aid-lab-org/eTactileKit/1_Hardware/04_Resources/Capture1.PNG

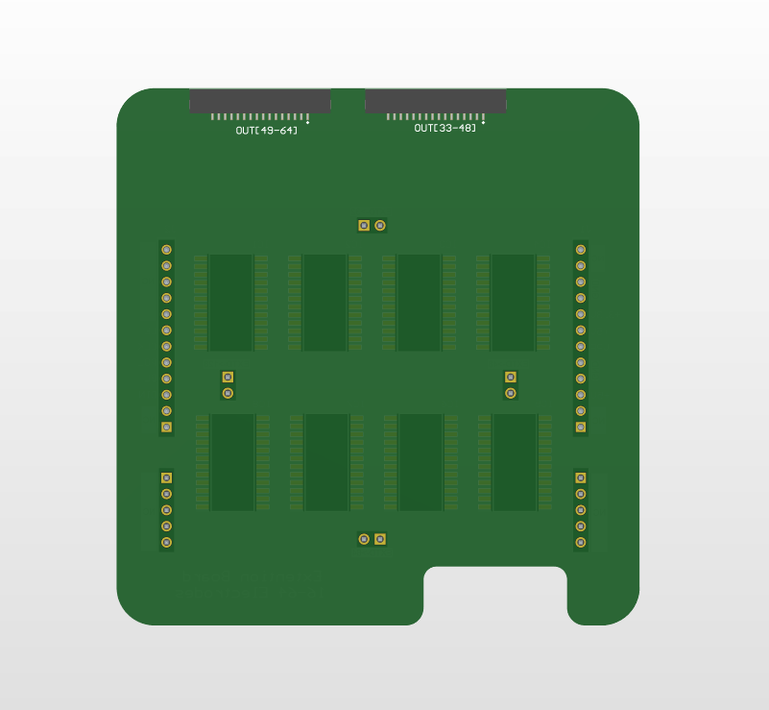
1_Hardware/04_Resources/Capture1.PNG
