aid-lab-org/eTactileKit/1_Hardware/04_Resources/Capture5.PNG

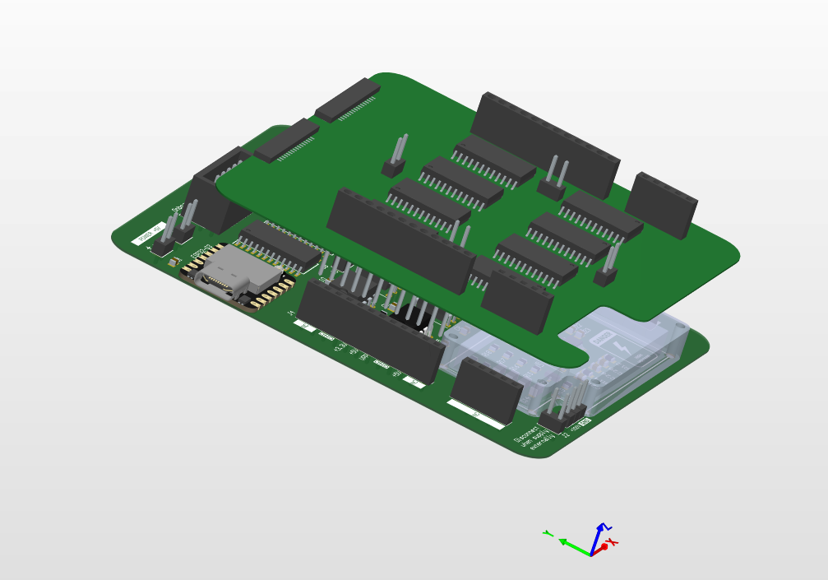
1_Hardware/04_Resources/Capture5.PNG
