aid-lab-org/eTactileKit/1_Hardware/04_Resources/Capture.PNG

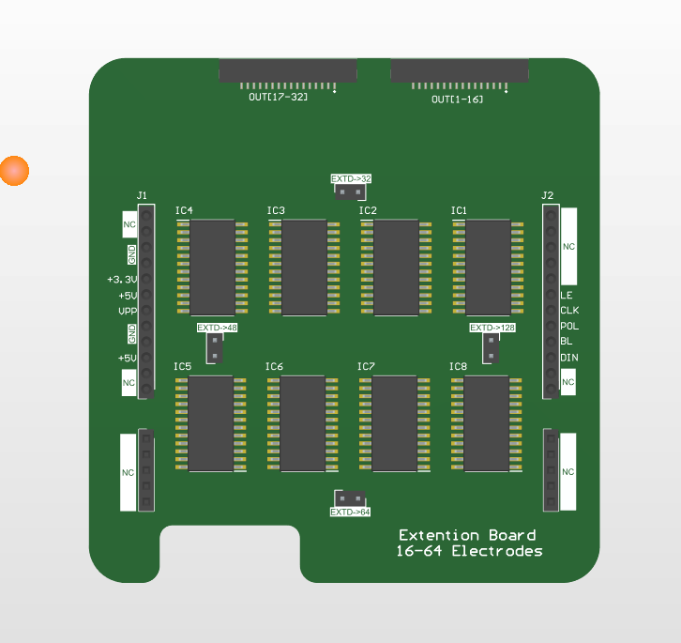
1_Hardware/04_Resources/Capture.PNG
