aid-lab-org/eTactileKit/8_Documentation/4_processing_gui/GUI.gif

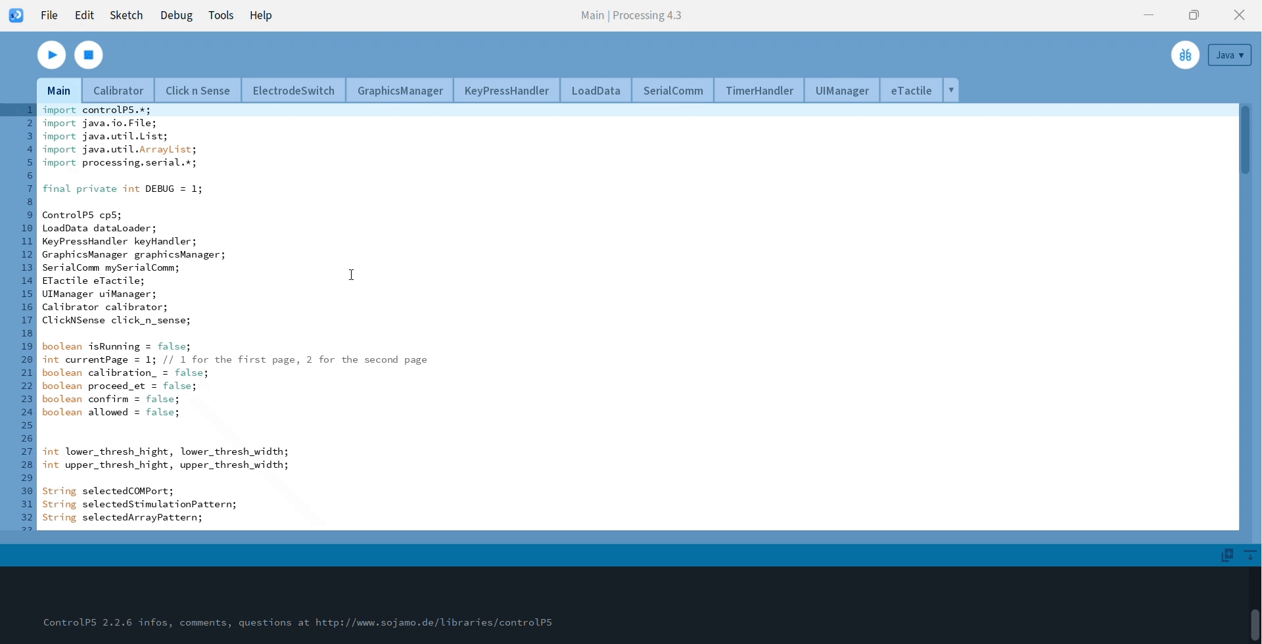
8_Documentation/4_processing_gui/GUI.gif
