aid-lab-org/eTactileKit/3_Electrode_Design_Tool/3_FabricationTool_App/images/finger_top.jpg

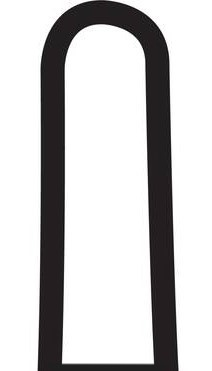
3_Electrode_Design_Tool/3_FabricationTool_App/images/finger_top.jpg
