aid-lab-org/eTactileKit/3_Electrode_Design_Tool/3_FabricationTool_App/images/Finger_Wrap_1.png

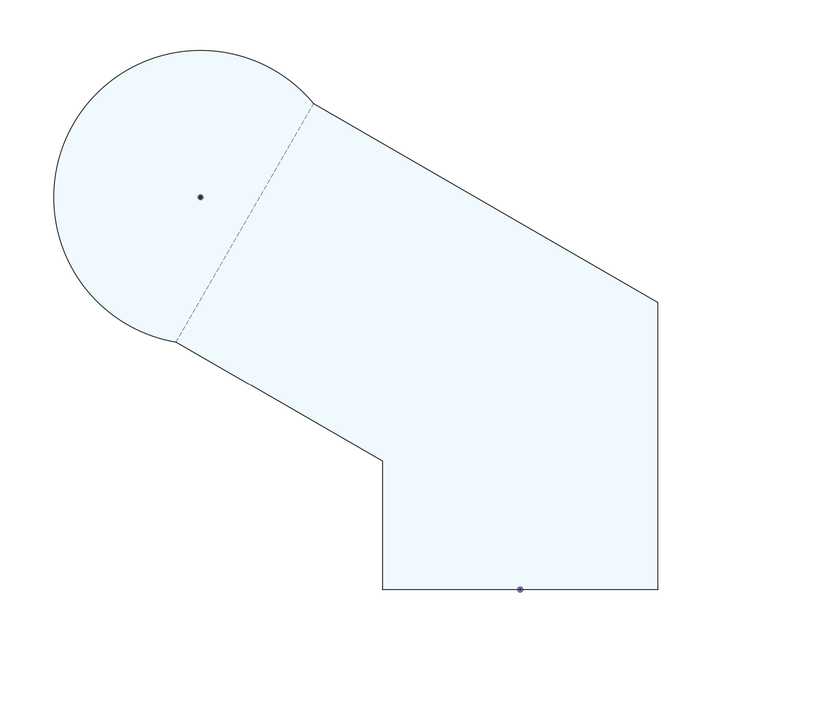
3_Electrode_Design_Tool/3_FabricationTool_App/images/Finger_Wrap_1.png
