aid-lab-org/eTactileKit/1_Hardware/04_Resources/Main_Controller_Schematic.pdf

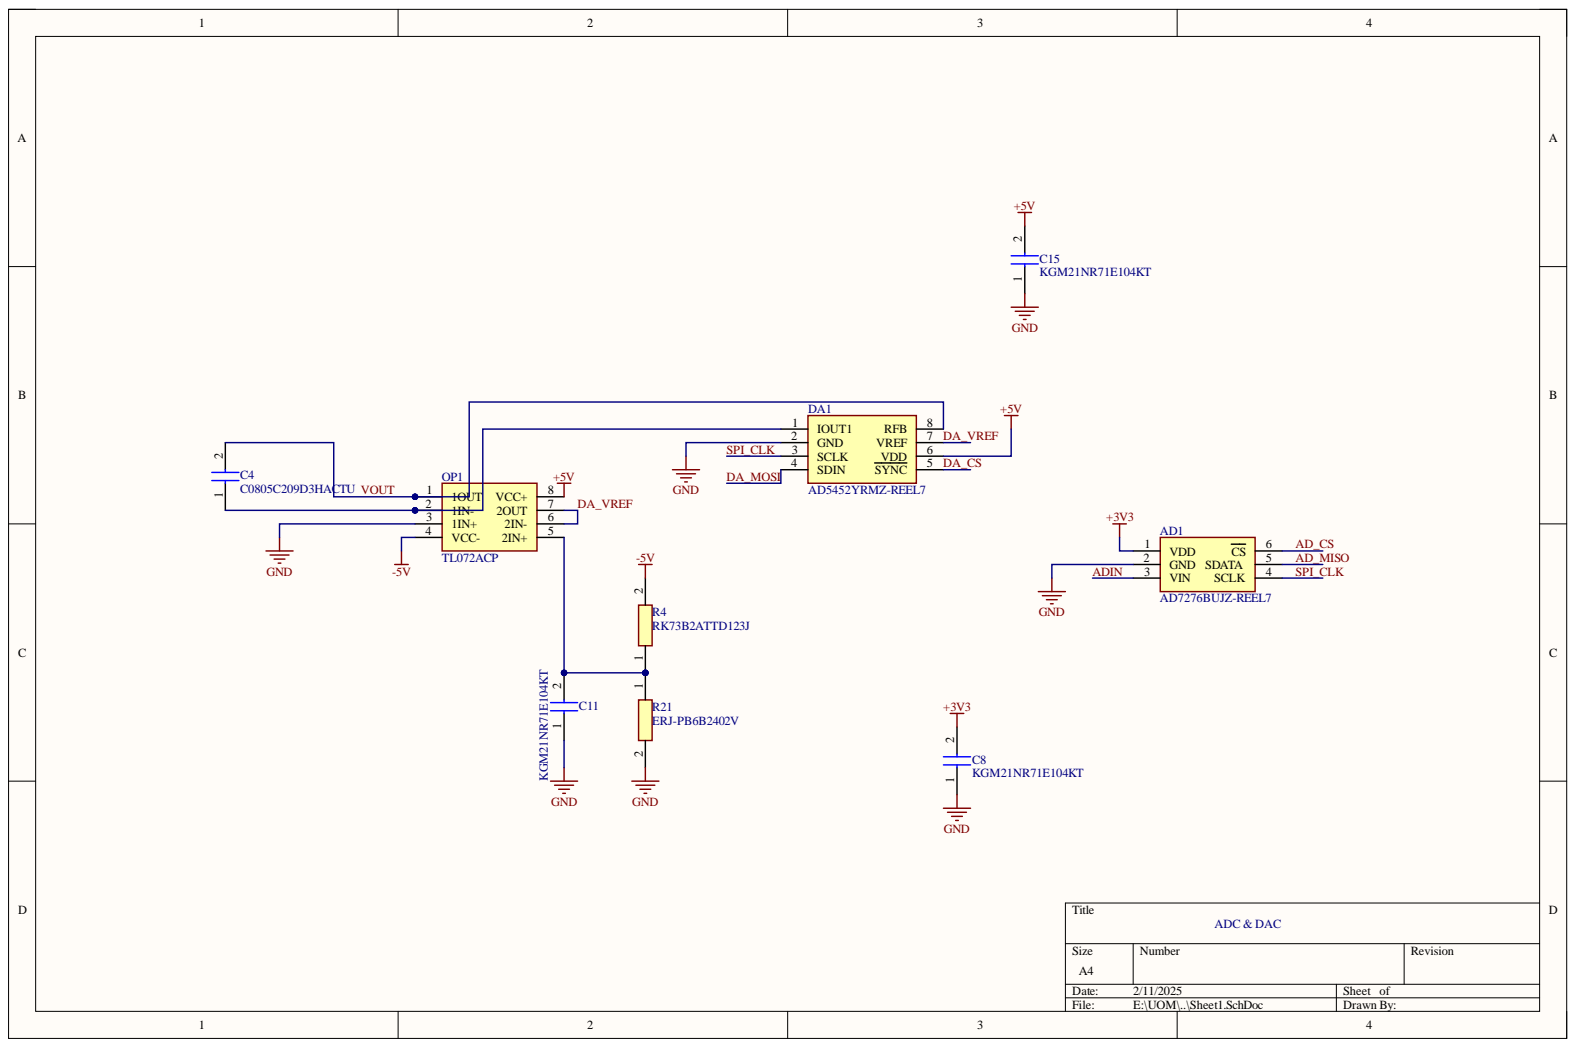
[picture p94: page 1]

Siz e A4 | Numb e r | R evisio n

Da te : 2/11/202 5 | She et of
File : E:\UOM\. .\She et1 . S c hD o c | Dr awn B y :

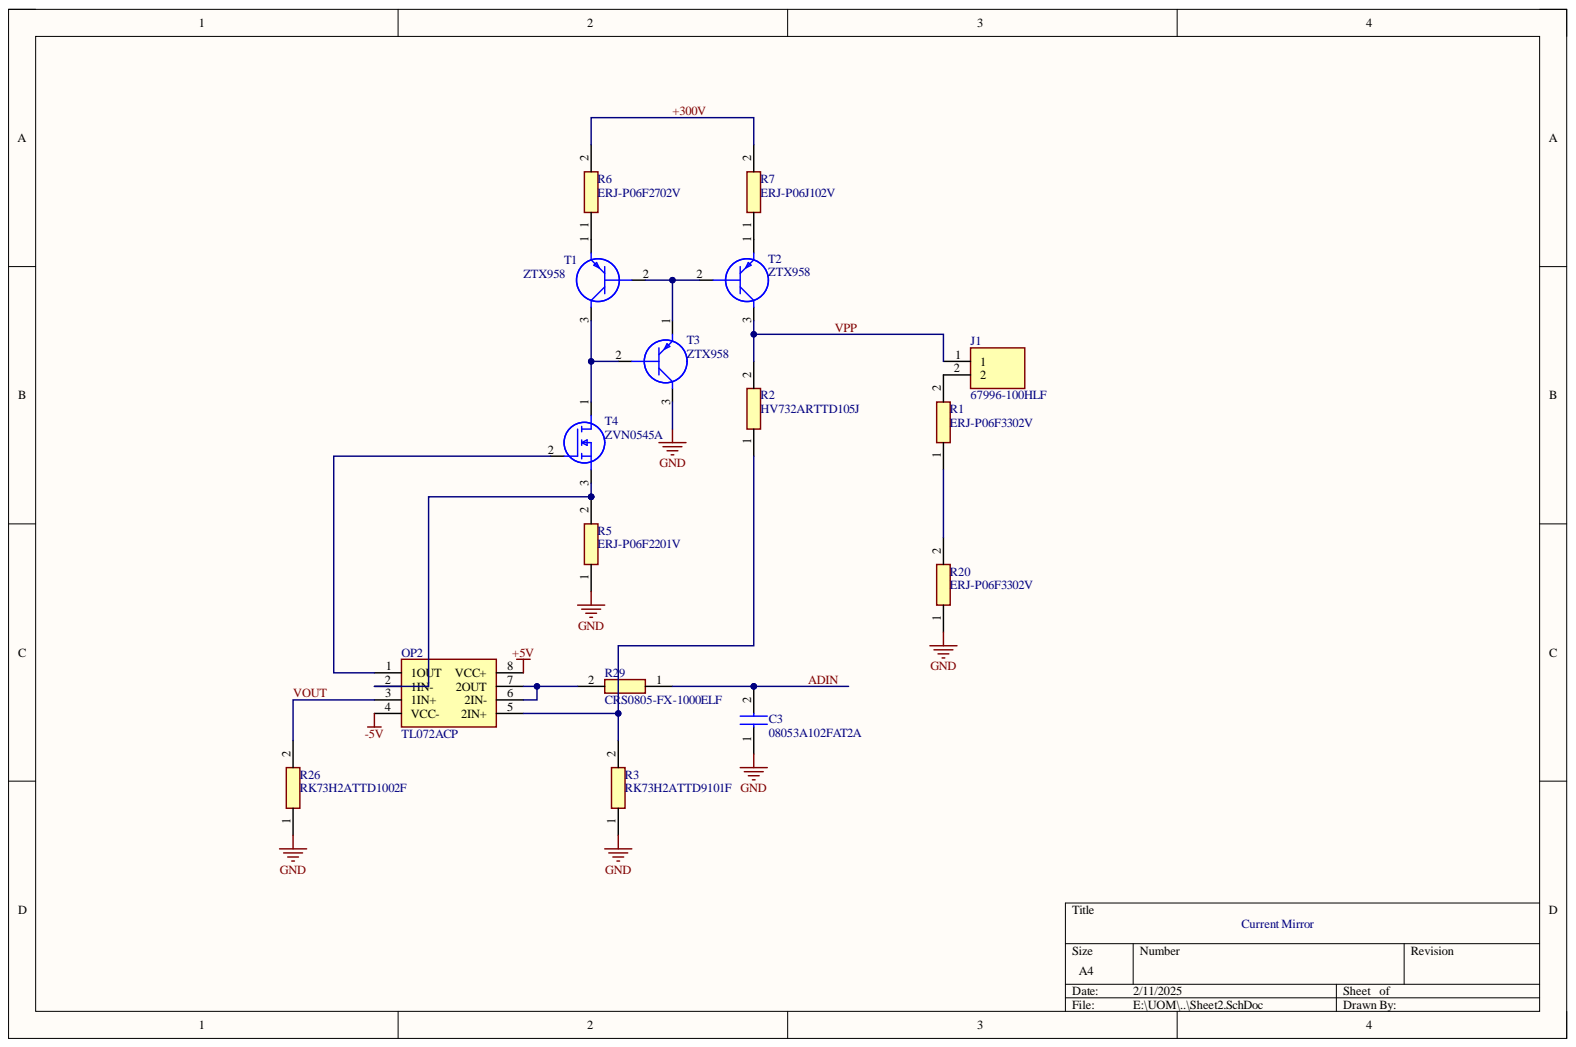
[picture p95: page 2]

Siz e A4 | Numb e r | R evisio n

Da te : 2/11/202 5 | She et of
File : E:\UOM\. .\She et2 . S c hD o c | Dr awn B y :

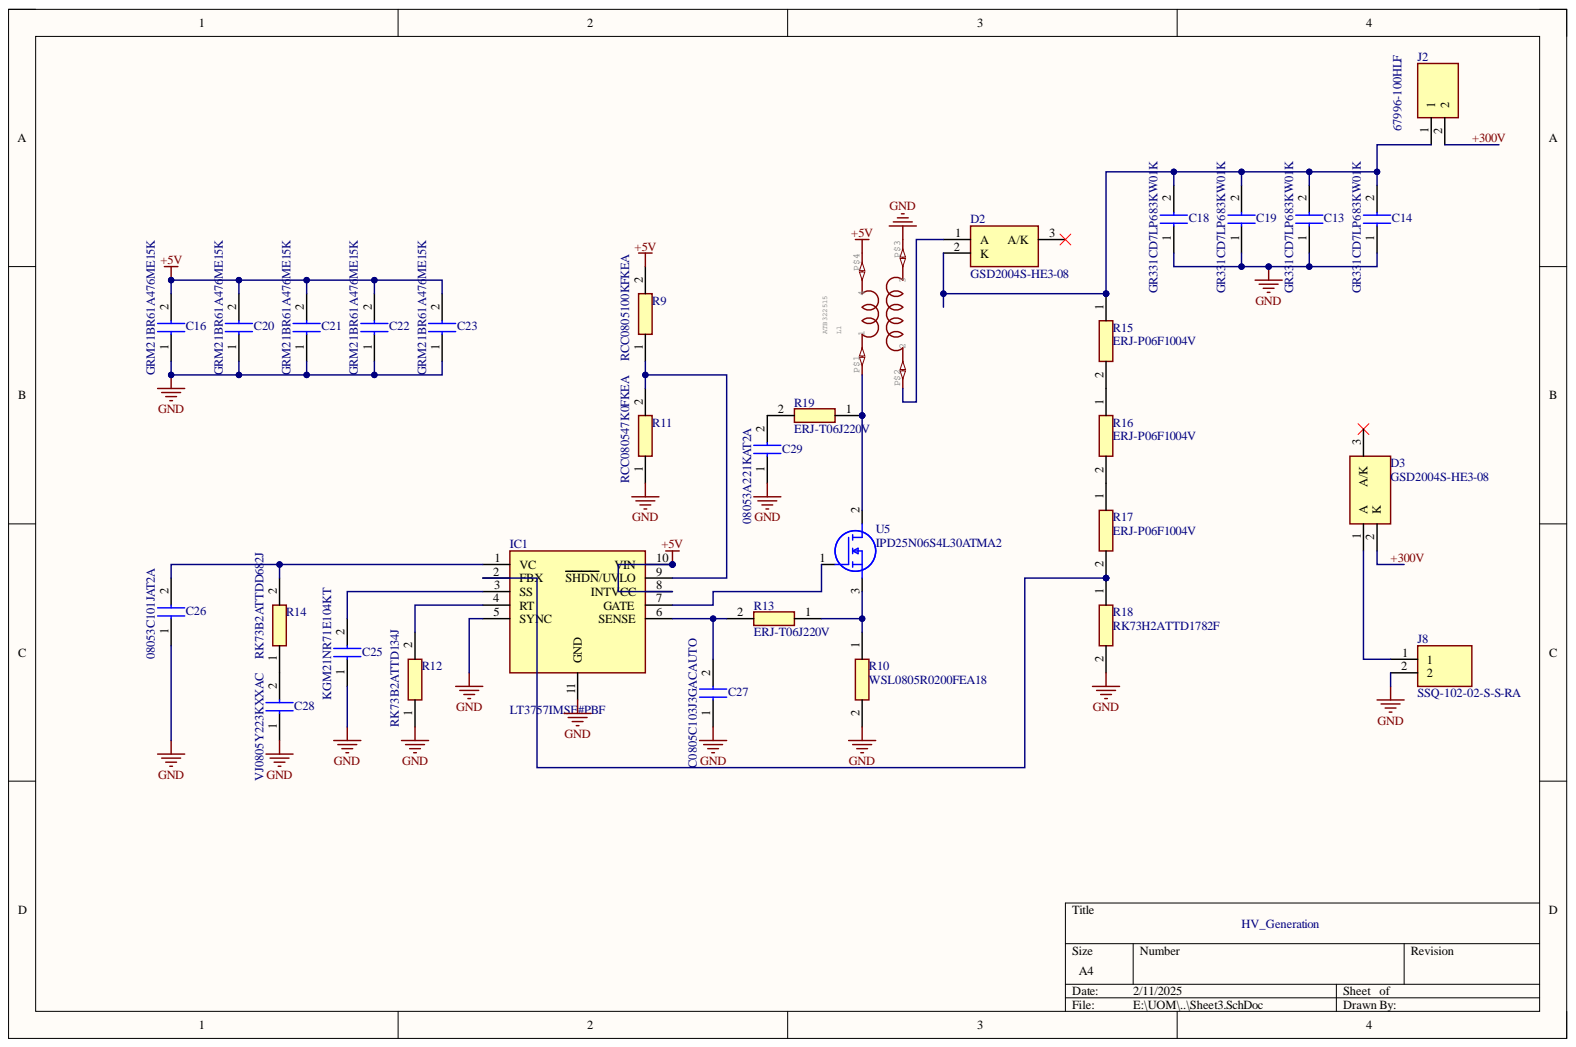
[picture p96: page 3]

Siz e A4 | Numb e r | R evisio n

Da te : 2/11/202 5 | She et of
File : E:\UOM\. .\She et3 . S c hD o c | Dr awn B y :

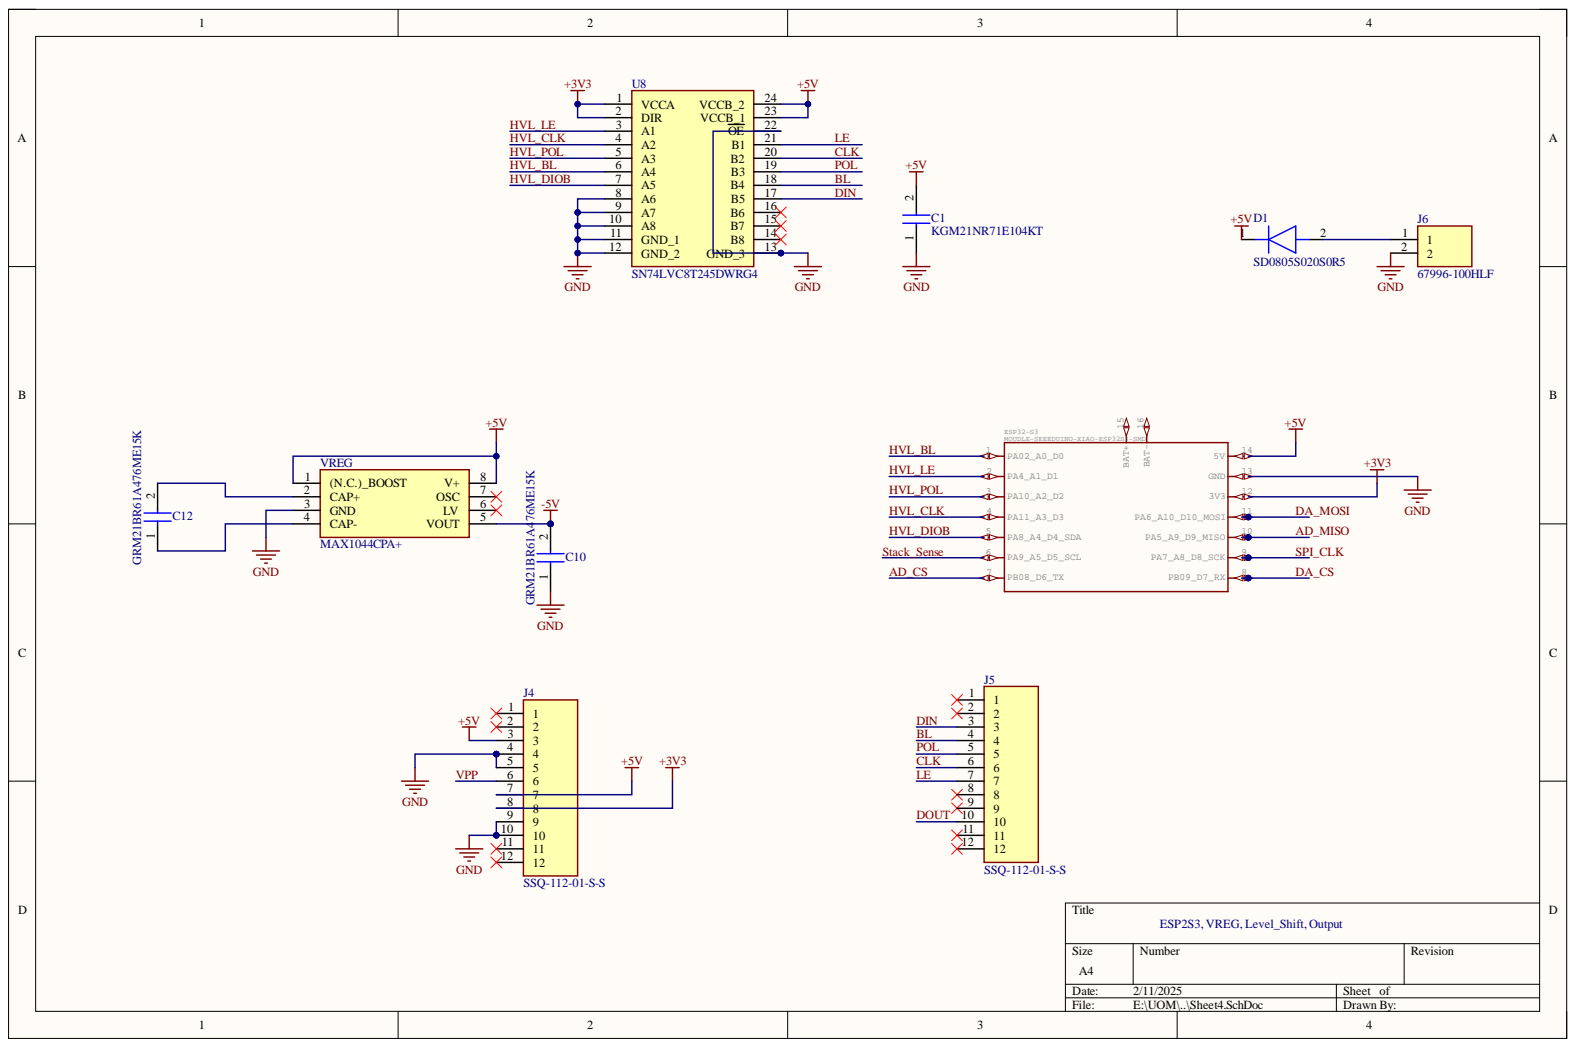
[picture p97: page 4]

CAP+ 2 OSC | 7

CAP- 4

Size A4 | Number | Revision

Date: 2/11/2025 | Sheet of
File: E:\UOM\..\Sheet4.SchDoc | Drawn By:

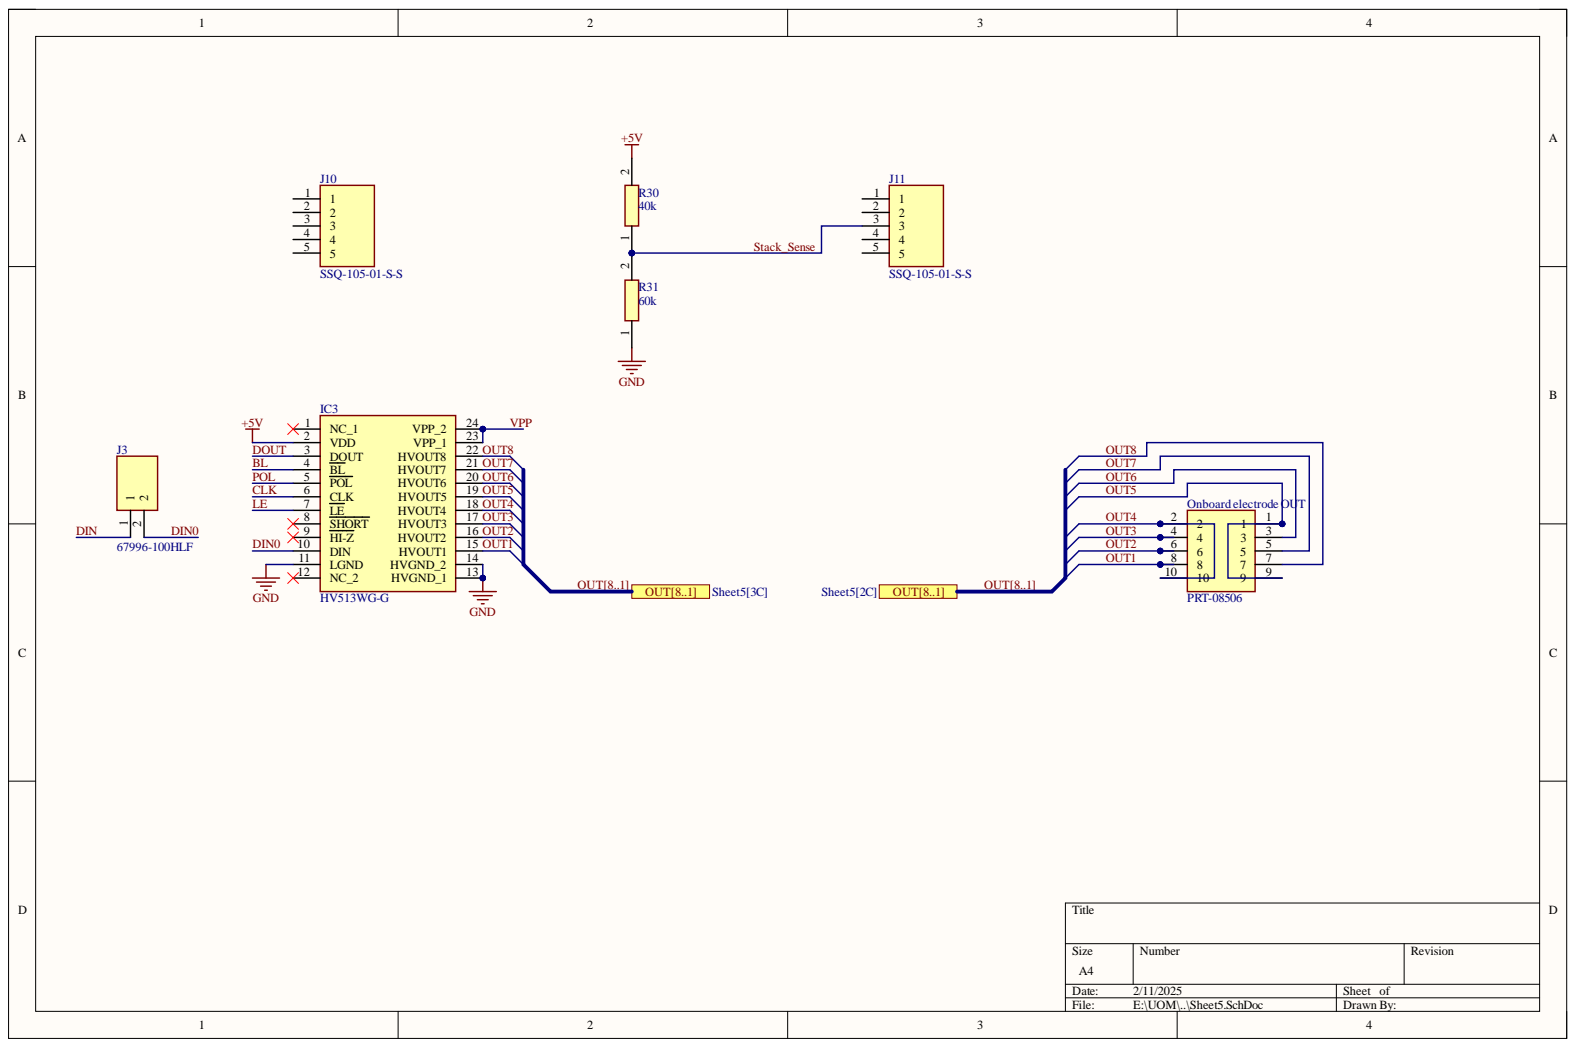
[picture p98: page 5]

Siz e A4 | Numb e r | R evisio n

Da te : 2/11/202 5 | She et of
File : E:\UOM\. .\She et5 . S c hD o c | Dr awn B y :

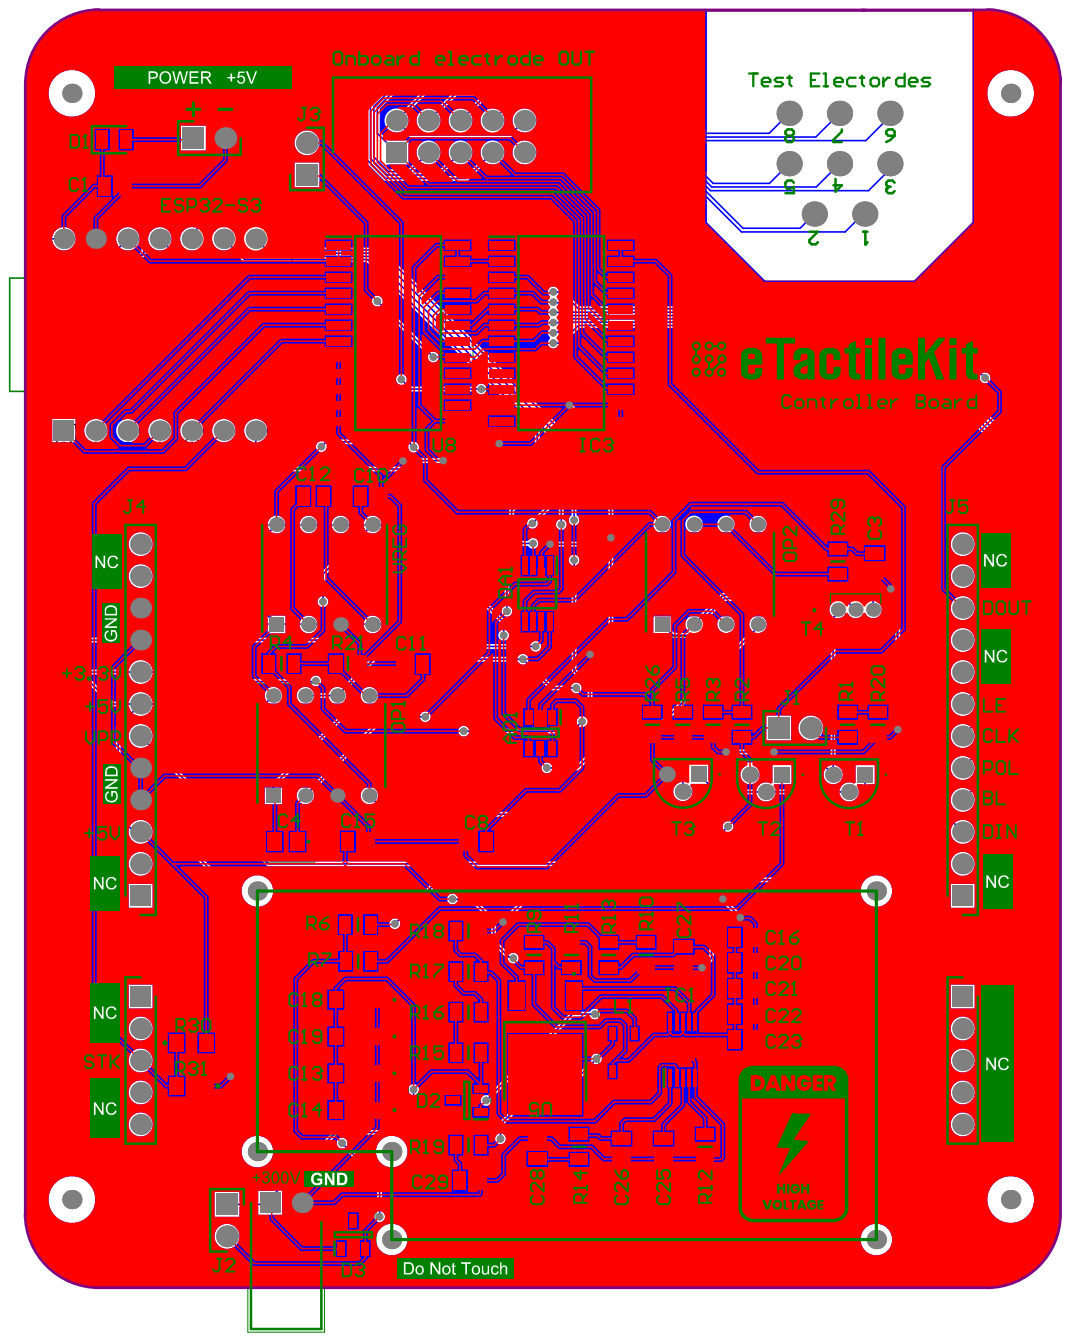
[picture p99: page 6]
