aid-lab-org/eTactileKit/1_Hardware/04_Resources/Switching_PCB_Schematic.pdf

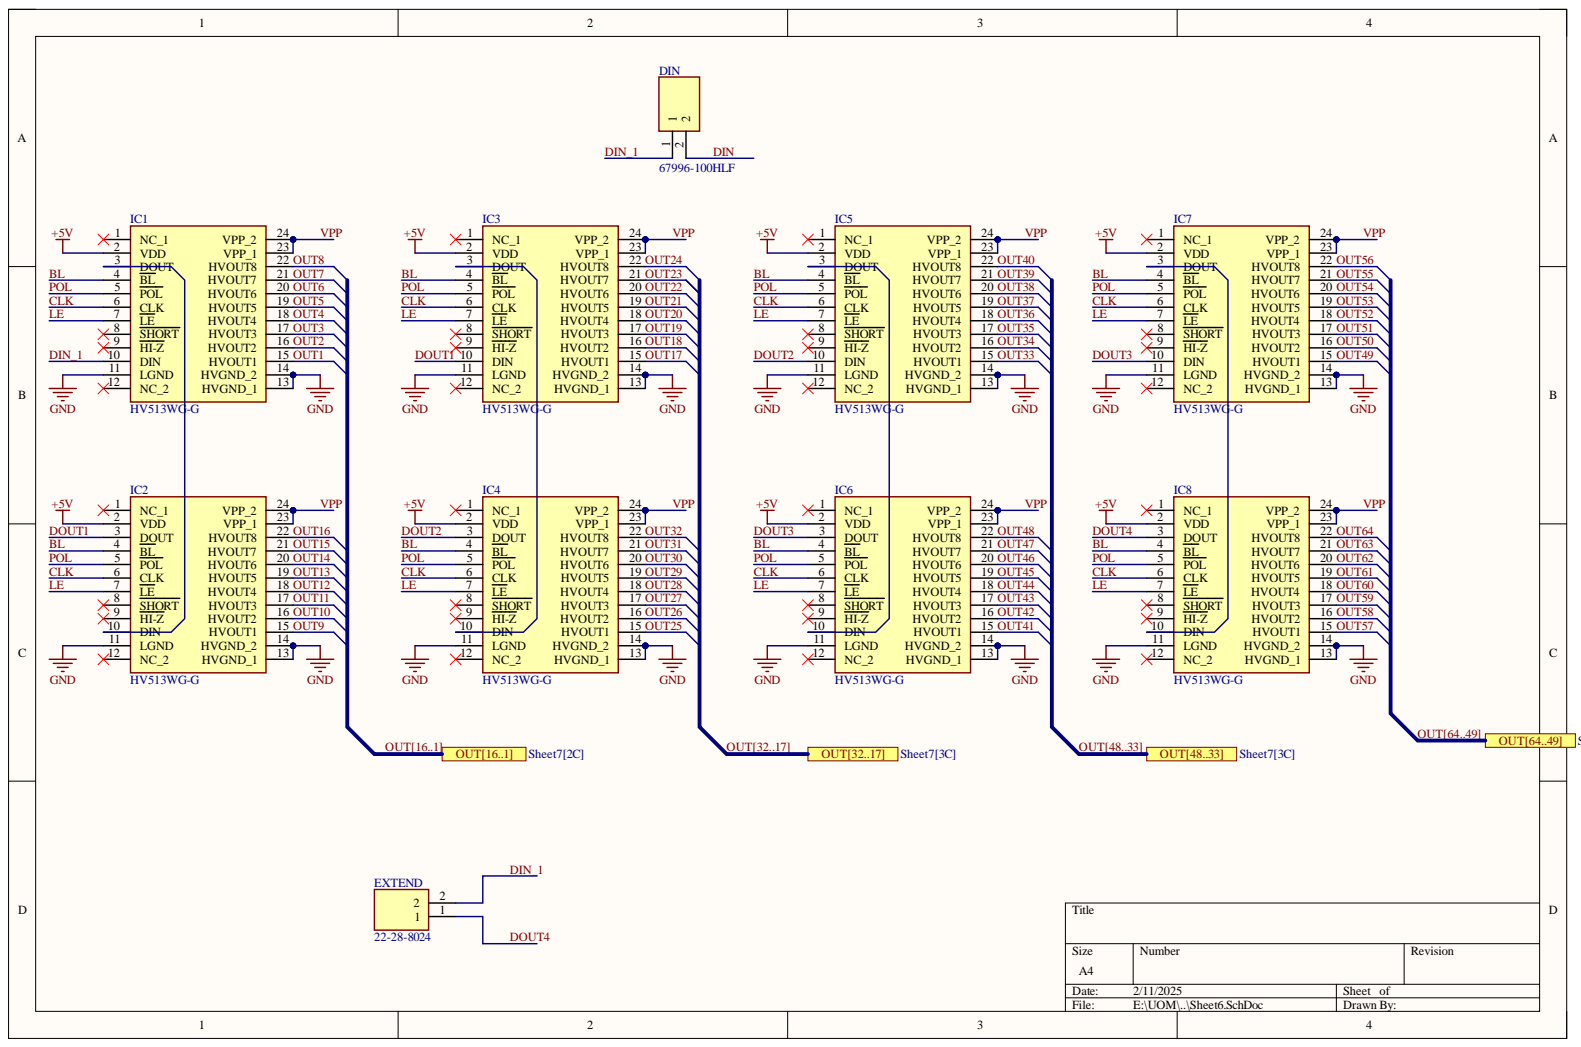
[picture p100: page 1]

DOUT4

Size A4 | Number | Revision

Date: 2/11/2025 | Sheet of
File: E:\UOM\..\Sheet6.SchDoc | Drawn By:

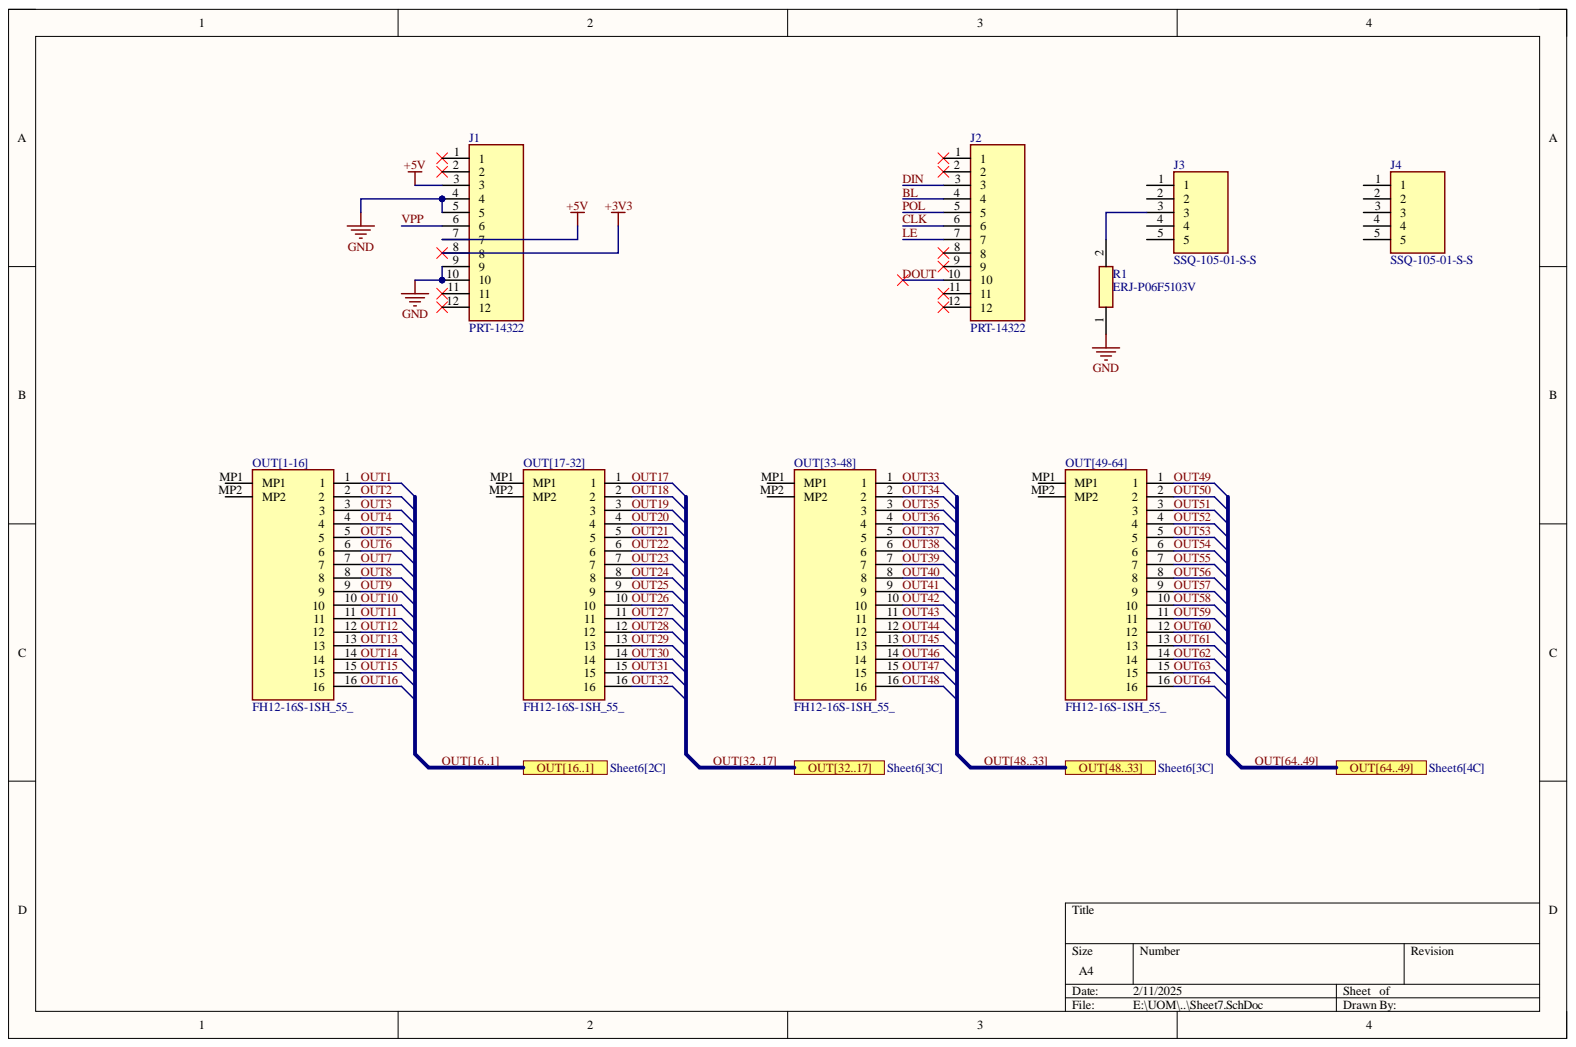
[picture p101: page 2]

Size A4 | Number | Revision

Date: 2/11/2025 | Sheet of
File: E:\UOM\..\Sheet7.SchDoc | Drawn By:

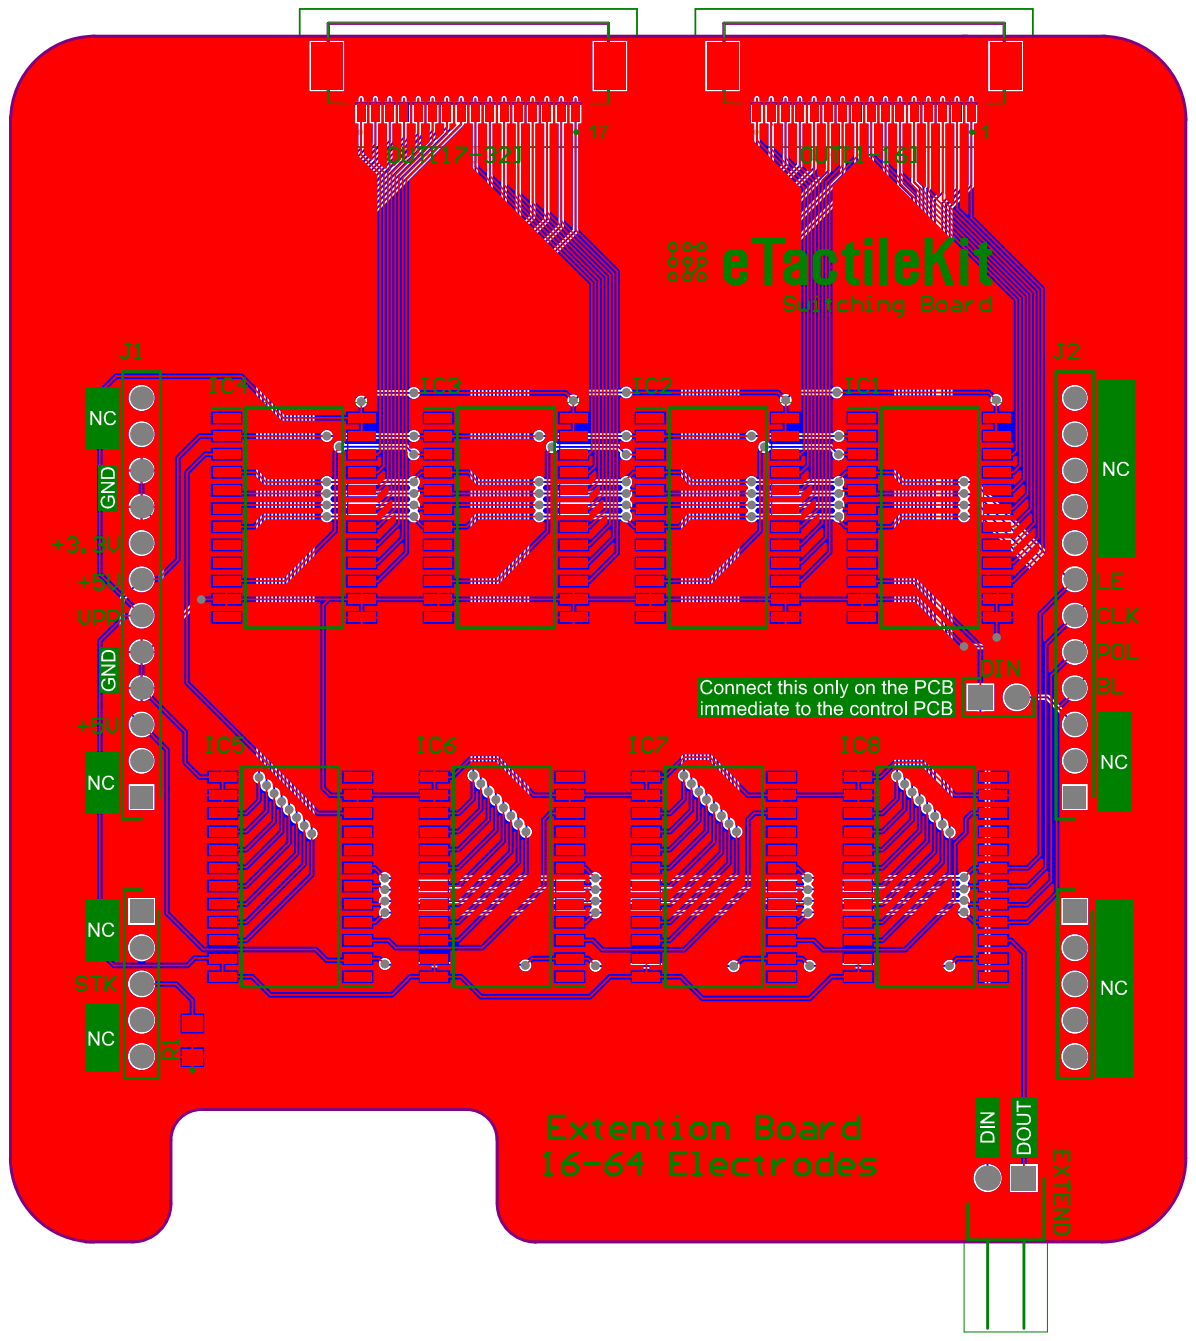
[picture p102: page 3]
